darkyden/Darkyden_project/Librairy/C0805C222K3GECTU/AltiumDesigner/CAPC480350_110N_KEM.step

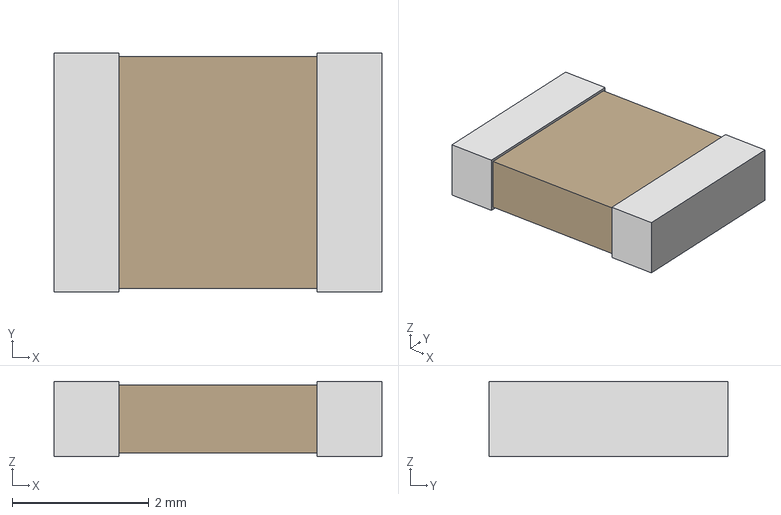
[picture p13: CAD file, 2025-04-21]
Librairy/C0805C222K3GECTU/AltiumDesigner/CAPC480350_110N_KEM.step
4.80 x 3.50 x 1.10 mm
