darkyden/Darkyden_project/Librairy/CGA4J3X5R1H475K125AB/AltiumDesigner/CAP_2012_TDK.step

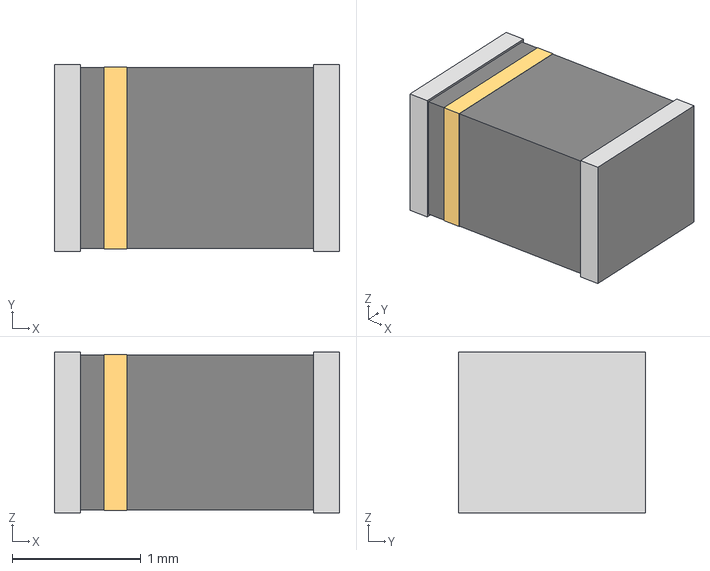
[picture p14: CAD file, 2025-04-21]
Librairy/CGA4J3X5R1H475K125AB/AltiumDesigner/CAP_2012_TDK.step
2.21 x 1.45 x 1.25 mm
