darkyden/Darkyden_project/Librairy/ECS_250_8_37B2_RWY_TR/ECS-250-8-37B2-RWY-TR.STEP

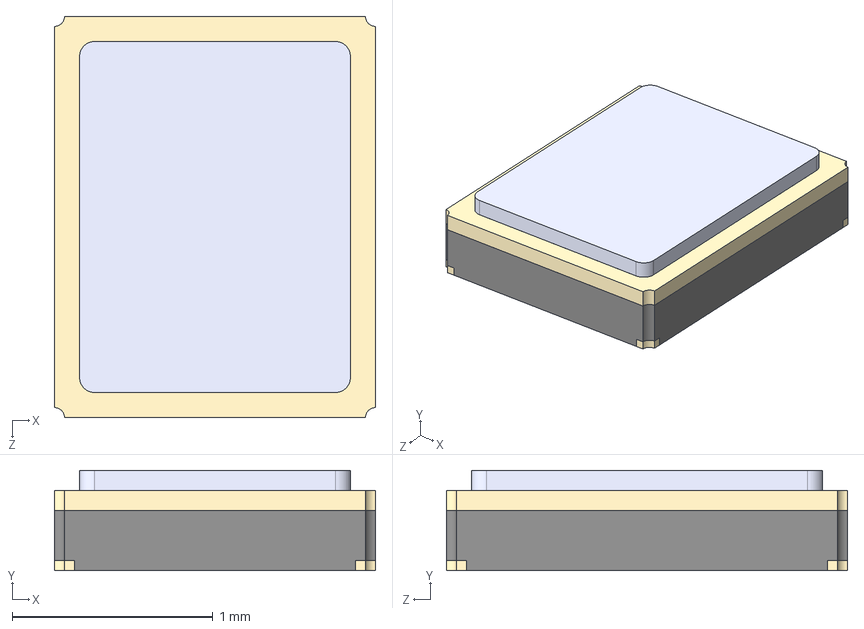
[picture p15: CAD file, 2025-04-13]
Librairy/ECS_250_8_37B2_RWY_TR/ECS-250-8-37B2-RWY-TR.STEP
1.60 x 0.5 x 2.00 mm
