darkyden/Darkyden_project/Librairy/ERA_3AEB472V/RC0603N_PAN.step

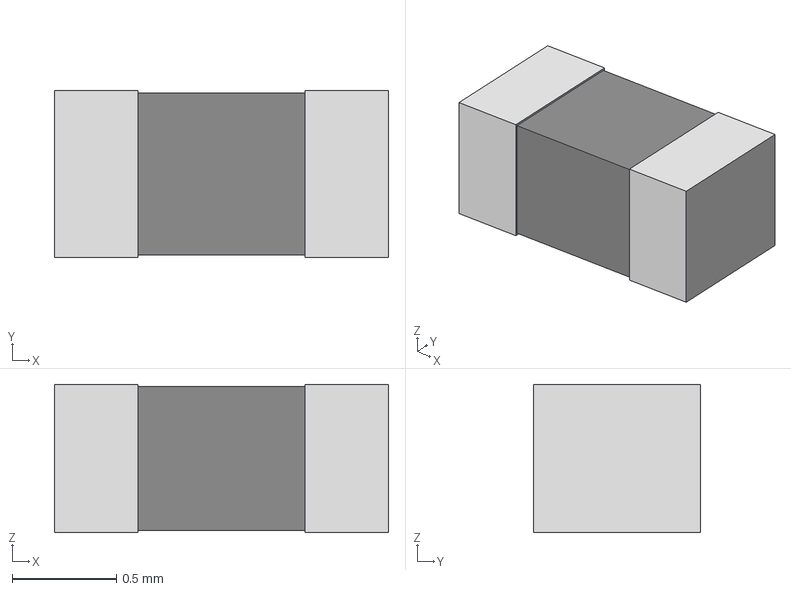
[picture p16: CAD file, 2025-04-21]
Librairy/ERA_3AEB472V/RC0603N_PAN.step
1.60 x 0.8 x 0.711 mm
