darkyden/Darkyden_project/Librairy/hdmi_mini/Download_STP_685119136923_rev1.stp

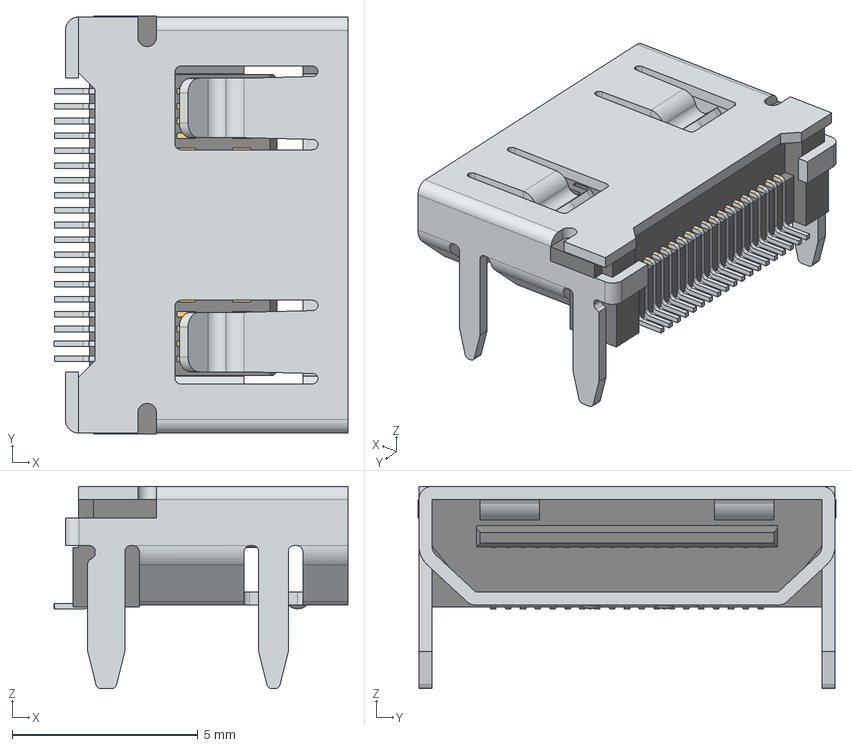
[picture p17: CAD file, 2025-04-25]
Librairy/hdmi_mini/Download_STP_685119136923_rev1.stp
7.90 x 11.2 x 5.45 mm
685119136923_Housing
685119136923_Shielding
685119136923_Housing2
685119136923_Pin1 x 18
685119136923_Pin2
