darkyden/Darkyden_project/Librairy/L829_1J1T_JM/L829-1J1T-JM.stp

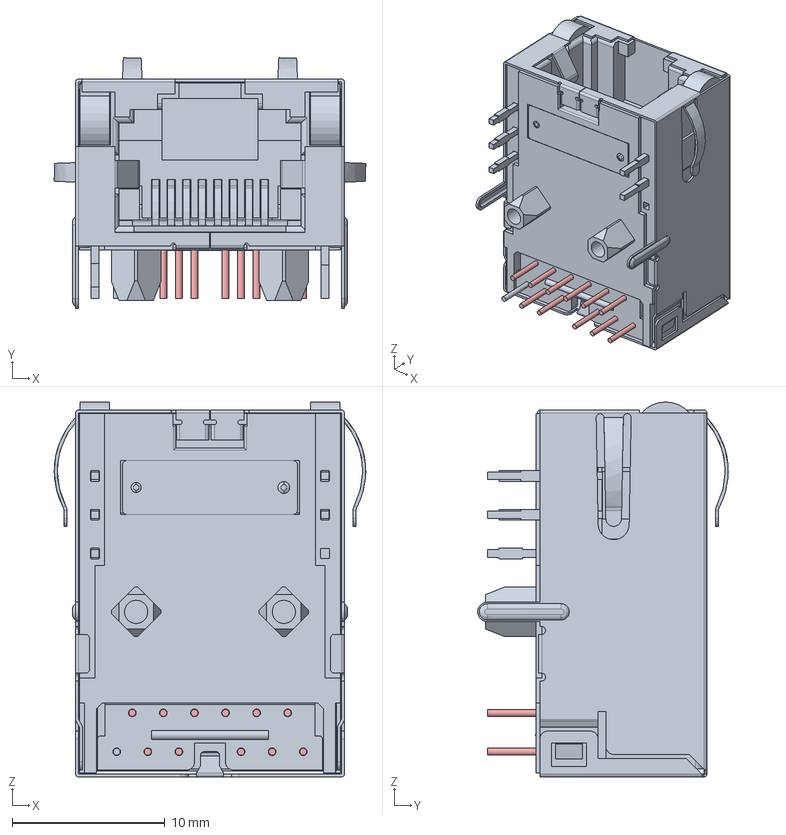
[picture p18: CAD file, 2025-04-11]
Librairy/L829_1J1T_JM/L829-1J1T-JM.stp
20.4 x 16.4 x 24.5 mm
L829-1J1T-JM_PART1
L829-1J1T-JM_PART2
L829-1J1T-JM_PART3
L829-1J1T-JM_PART4
L829-1J1T-JM_PART5
L829-1J1T-JM_PART6
L829-1J1T-JM_PART7
L829-1J1T-JM_PART8
L829-1J1T-JM_PART9
L829-1J1T-JM_PART10
L829-1J1T-JM_PART11
L829-1J1T-JM_PART12
L829-1J1T-JM_PART13
L829-1J1T-JM_PART14
L829-1J1T-JM_PART15
L829-1J1T-JM_PART16
L829-1J1T-JM_PART17
L829-1J1T-JM_PART18
L829-1J1T-JM_PART19
L829-1J1T-JM_PART20
L829-1J1T-JM_PART21
L829-1J1T-JM_PART22
L829-1J1T-JM_PART23
L829-1J1T-JM_PART24
L829-1J1T-JM_PART25
L829-1J1T-JM_PART26
