darkyden/Darkyden_project/Librairy/MDT420M03001/MDT420M03001.STEP

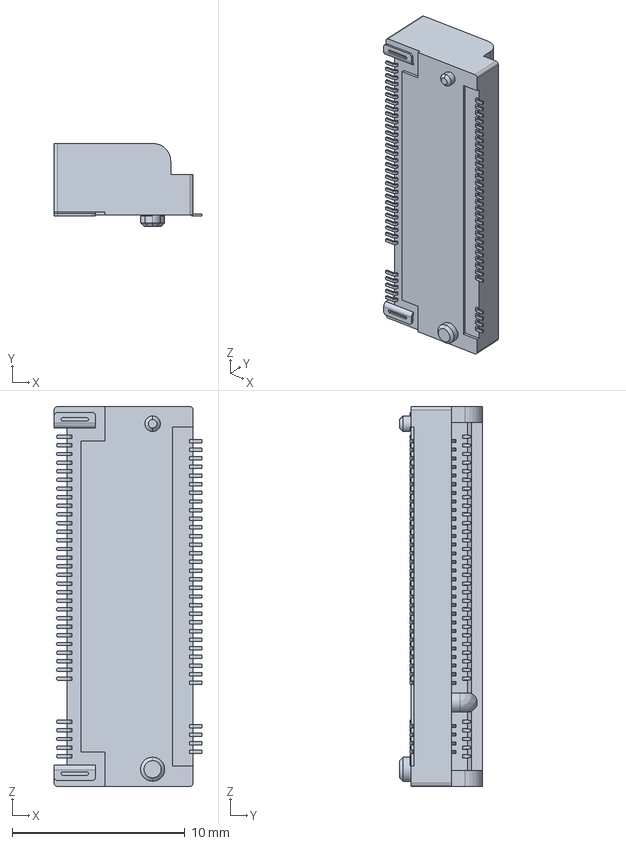
[picture p19: CAD file, 2025-04-11]
Librairy/MDT420M03001/MDT420M03001.STEP
8.55 x 4.80 x 22.0 mm
