darkyden/Darkyden_project/Librairy/MWSA0603S_XRXMT/AltiumDesigner/IND_MWSA0603S_SNL.step

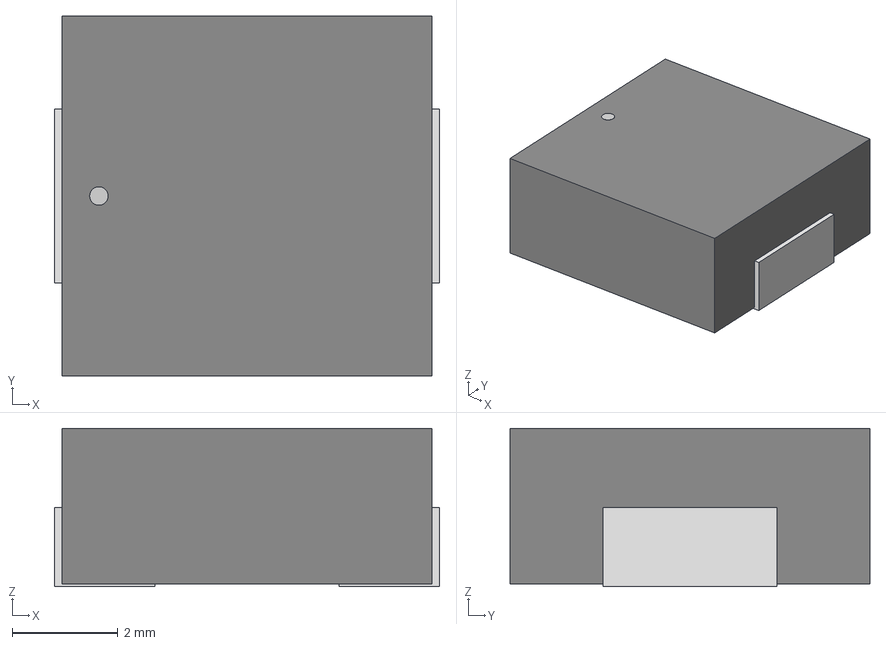
[picture p20: CAD file, 2025-04-14]
Librairy/MWSA0603S_XRXMT/AltiumDesigner/IND_MWSA0603S_SNL.step
7.29 x 6.81 x 3.00 mm
