darkyden/Darkyden_project/Librairy/PI6C557_05BLE/AltiumDesigner/L20_PER.step

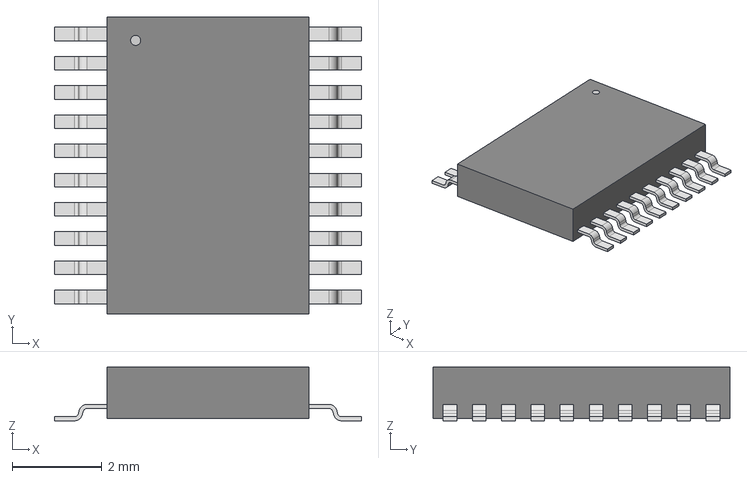
[picture p21: CAD file, 2025-04-11]
Librairy/PI6C557_05BLE/AltiumDesigner/L20_PER.step
6.83 x 6.60 x 1.20 mm
