darkyden/Darkyden_project/Librairy/RES_SMD_0603/RES_SMD_0603.step

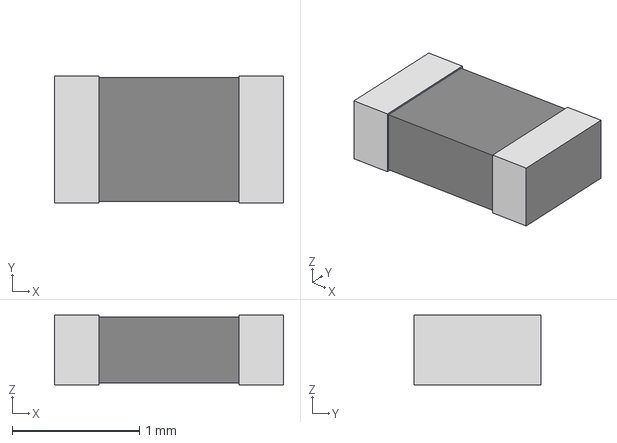
[picture p22: CAD file, 2025-04-09]
Librairy/RES_SMD_0603/RES_SMD_0603.step
1.80 x 1.00 x 0.55 mm
