darkyden/Darkyden_project/Librairy/RT9193_33GB/SOT-23-5_RIT.step

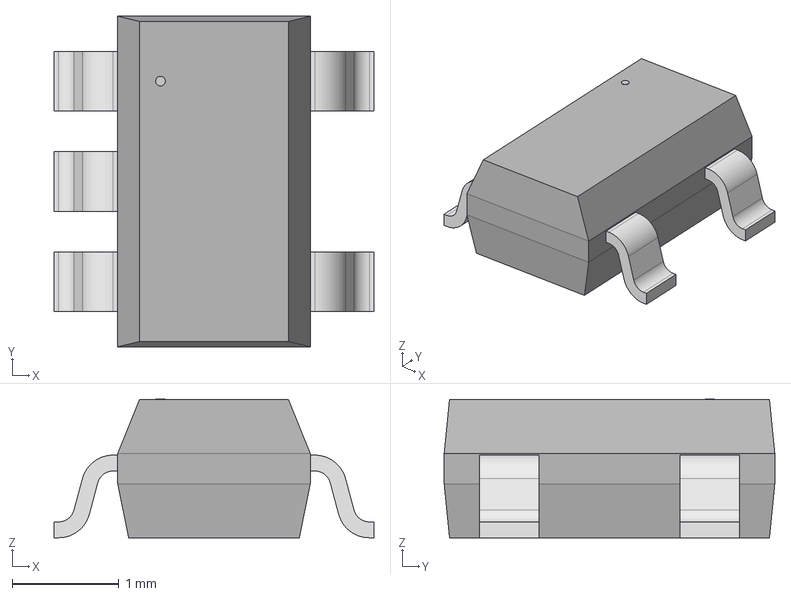
[picture p23: CAD file, 2025-04-13]
Librairy/RT9193_33GB/SOT-23-5_RIT.step
3.00 x 3.10 x 1.30 mm
