darkyden/Darkyden_project/Librairy/rtc-bat/BH-49A-5-T-BK_ADM.step

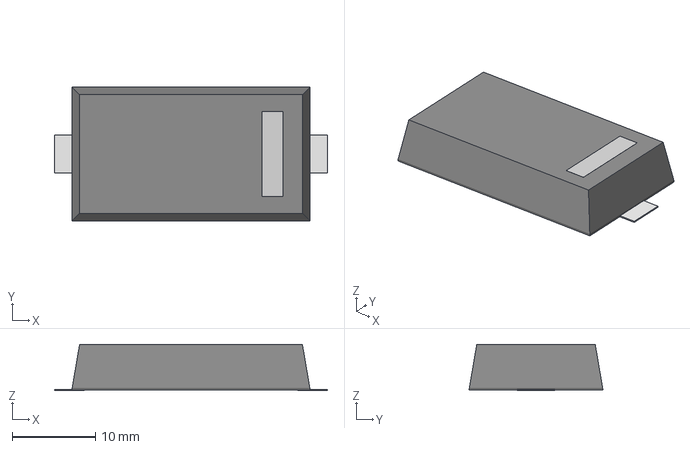
[picture p24: CAD file, 2025-04-14]
Librairy/rtc-bat/BH-49A-5-T-BK_ADM.step
32.7 x 16.0 x 5.52 mm
