darkyden/Darkyden_project/Librairy/S2B-PH-K-S.STEP

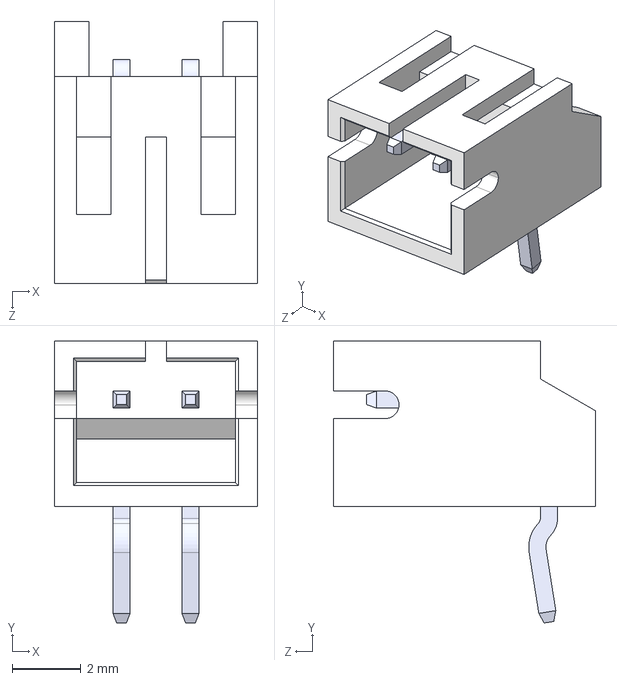
[picture p25: CAD file, 2025-05-05]
Librairy/S2B-PH-K-S.STEP
5.90 x 8.18 x 7.60 mm
