darkyden/Darkyden_project/Librairy/SY6280AAC/SOT23-5_SGY.step

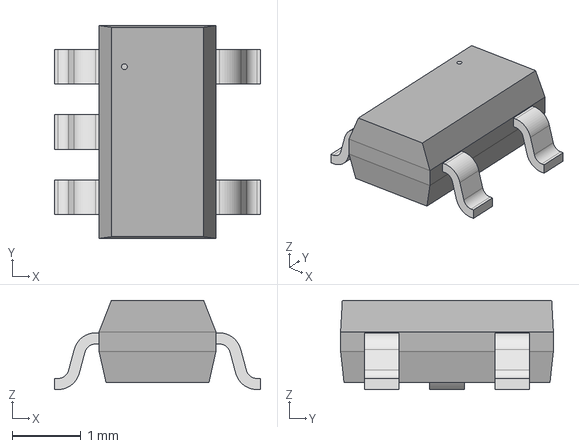
[picture p26: CAD file, 2025-04-09]
Librairy/SY6280AAC/SOT23-5_SGY.step
3.00 x 3.10 x 1.30 mm
