darkyden/Darkyden_project/Librairy/test_point/New folder/5006.STEP

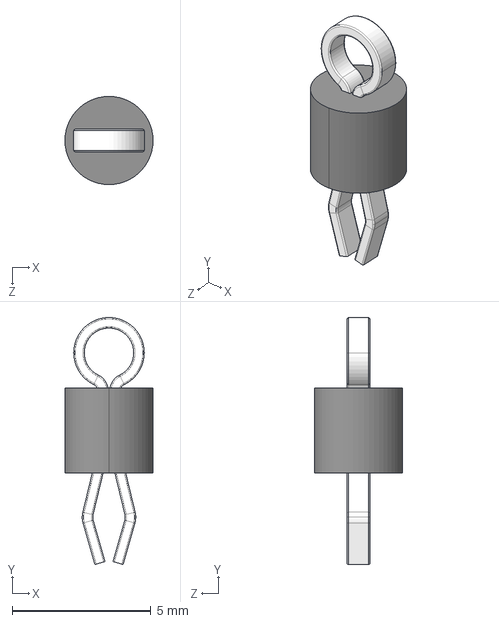
[picture p27: CAD file, 2025-04-11]
Librairy/test_point/New folder/5006.STEP
3.17 x 8.89 x 3.17 mm
