darkyden/Darkyden_project/Librairy/TPD4E02B04DQAR/DQA0010A.stp

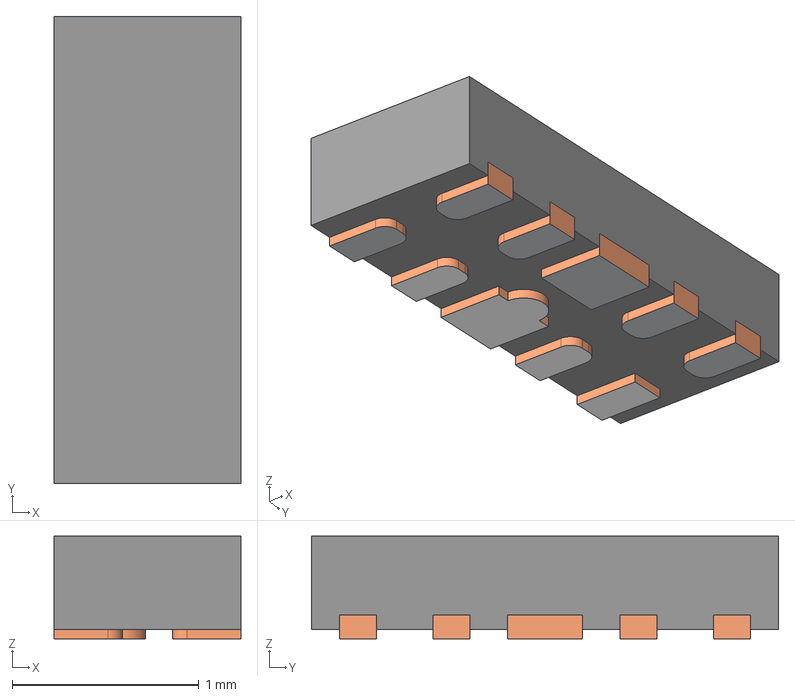
[picture p28: CAD file, 2025-04-09]
Librairy/TPD4E02B04DQAR/DQA0010A.stp
1.00 x 2.50 x 0.55 mm
BODY-SON
FRAME-DQA0010A
PIN1-ID
