darkyden/Darkyden_project/Librairy/TPS22917LDBVR/DBV0006A.stp

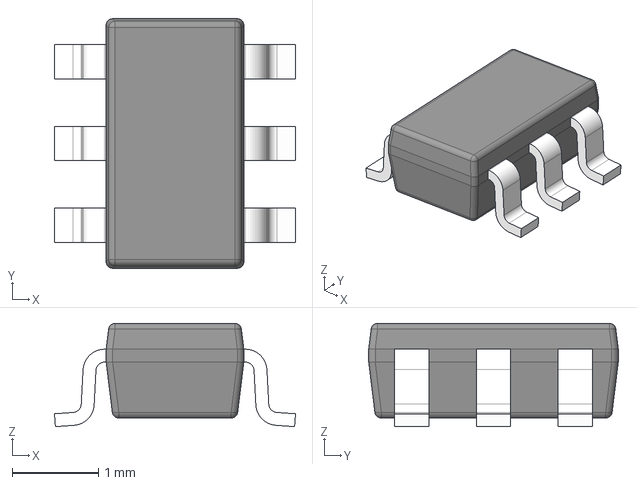
[picture p29: CAD file, 2025-04-11]
Librairy/TPS22917LDBVR/DBV0006A.stp
2.80 x 2.90 x 1.20 mm
BODY-SOT
LEAD-SOT x 6
