darkyden/Darkyden_project/Librairy/WPN4020H2R2MT/AltiumDesigner/IND_WPN4020H_SNL.step

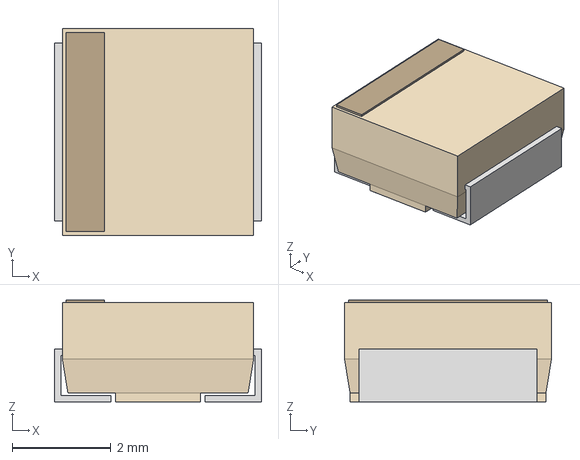
[picture p30: CAD file, 2025-04-14]
Librairy/WPN4020H2R2MT/AltiumDesigner/IND_WPN4020H_SNL.step
4.19 x 4.19 x 2.06 mm
