darkyden/Darkyden_project/Librairy/RAHHD19TR--3DModel-STEP-56544.STEP

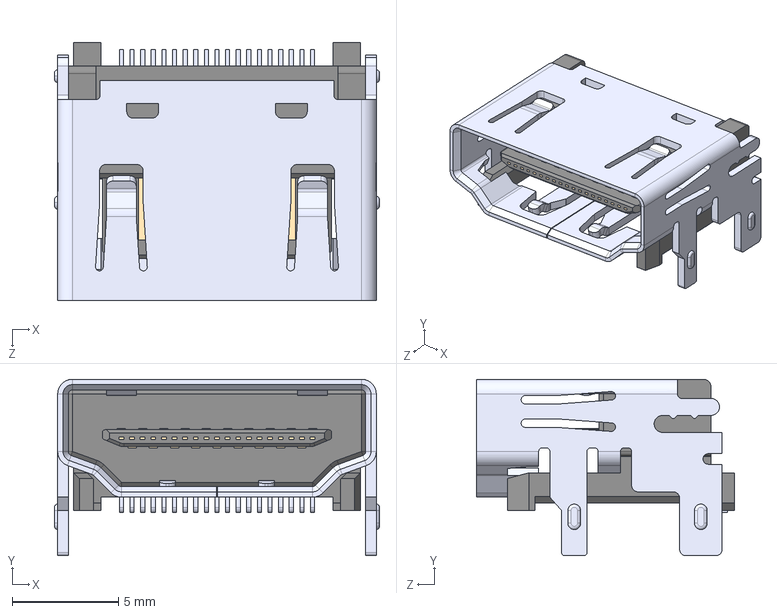
[picture p31: CAD file, 2025-04-25]
Librairy/RAHHD19TR--3DModel-STEP-56544.STEP
15.3 x 8.31 x 12.1 mm
