darkyden/Darkyden_project/PROG/lcd_interactive/pilote/piloteJeuReflex.c

//************************************************************************************
// Nom du fichier : piloteJeuReflex.c 
// Auteur : Harold Malbrouck 
//
// Date de création : 30 Mai 2025
//
// Description : Couche pilote pour le jeu de réflexe.
//               (Actuellement vide mais prête pour intégrer du code bas-niveau)
//************************************************************************************
#include "../include/piloteJeuReflex.h"

void piloteJeuReflex_initialiser() {
//************************************************************************************
// Initialise les éléments matériels du jeu de réflexe.
// Cette fonction est prévue pour gérer du matériel bas-niveau (buzzer, LED, etc.),
// mais reste vide pour le moment.
//************************************************************************************
    // Placeholder pour initialisation bas niveau (rien pour le moment)
}
